cl-ire/LED_Matrix_/src/backend/LEDMatrix/digits.py

   
digits = {
    "0": [
        [1,1,1],
        [1,0,1],
        [1,0,1],
        [1,0,1],
        [1,1,1]
    ],
    "1": [
        [0,0,1],
        [0,0,1],
        [0,0,1],
        [0,0,1],
        [0,0,1]
    ],
    "2": [
        [1,1,1],
        [0,0,1],
        [1,1,1],
        [1,0,0],
        [1,1,1]
    ],
    "3": [
        [1,1,1],
        [0,0,1],
        [1,1,1],
        [0,0,1],
        [1,1,1]
    ],
    "4": [
        [1,0,1],
        [1,0,1],
        [1,1,1],
        [0,0,1],
        [0,0,1]
    ],
    "5": [
        [1,1,1],
        [1,0,0],
        [1,1,1],
        [0,0,1],
        [1,1,1]
    ],
    "6": [
        [1,1,1],
        [1,0,0],
        [1,1,1],
        [1,0,1],
        [1,1,1]
    ],
    "7": [
        [1,1,1],
        [0,0,1],
        [0,1,0],
        [1,0,0],
        [1,0,0]
    ],
    "8": [
        [1,1,1],
        [1,0,1],
        [1,1,1],
        [1,0,1],
        [1,1,1]
    ],
    "9": [
        [1,1,1],
        [1,0,1],
        [1,1,1],
        [0,0,1],
        [1,1,1]
    ],
   "blank": [
        [0,0,0],
        [0,0,0],
        [0,0,0],
        [0,0,0],
        [0,0,0]
    ]
}    

weather_symbols = {
    "clear": [
        [[0,0,0],[0,0,0],[0,0,0],[0,0,0],[0,0,0],[0,0,0]],
        [[0,0,0],[0,0,0],[255,255,0],[0,0,0],[0,0,0],[0,0,0]],
        [[0,0,0],[255,255,0],[255,255,0],[255,255,0],[0,0,0],[0,0,0]],
        [[0,0,0],[0,0,0],[255,255,0],[0,0,0],[0,0,0],[0,0,0]],
        [[0,0,0],[0,0,0],[0,0,0],[0,0,0],[0,0,0],[0,0,0]],
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
        [[0,0,0],[255,255,0],[255,255,0],[255,255,0],[0,0,0],[0,0,0]],
        [[0,0,0],[0,0,0],[255,255,0],[0,0,0],[0,0,0],[0,0,0]],
        [[0,0,0],[0,0,0],[0,0,0],[0,0,0],[0,0,0],[0,0,0]],
        [[0,0,0],[0,0,0],[0,0,0],[0,0,0],[0,0,0],[0,0,0]]
    ]
}
